jonbobcar/tenkey_plusplus/documentation/tenkey++_default.png

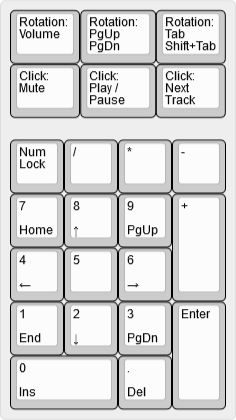
documentation/tenkey++_default.png
